ksaplabo-org/KsapSeatMotionSensor/img/システム構成図.png

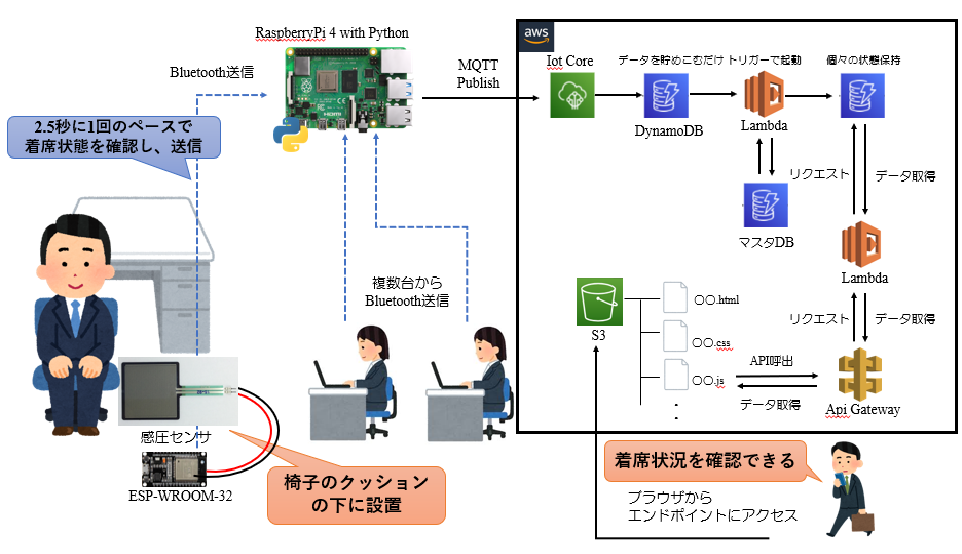
img/システム構成図.png
