ksaplabo-org/KsapSeatMotionSensor/img/感圧センサ.jpg

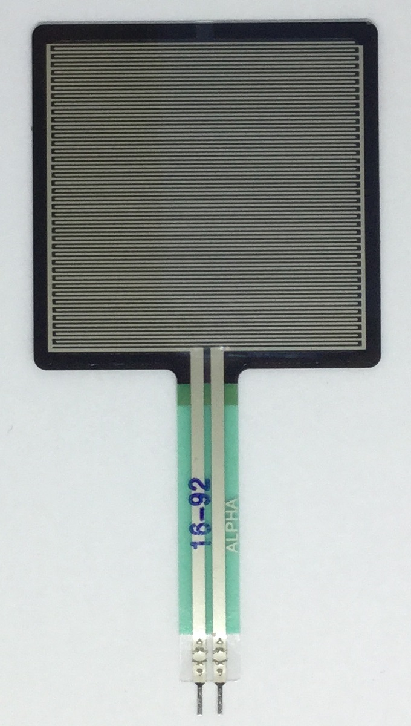
img/感圧センサ.jpg
