ksaplabo-org/KsapSeatMotionSensor/ksap-seatmotion/assets/img/外出.png

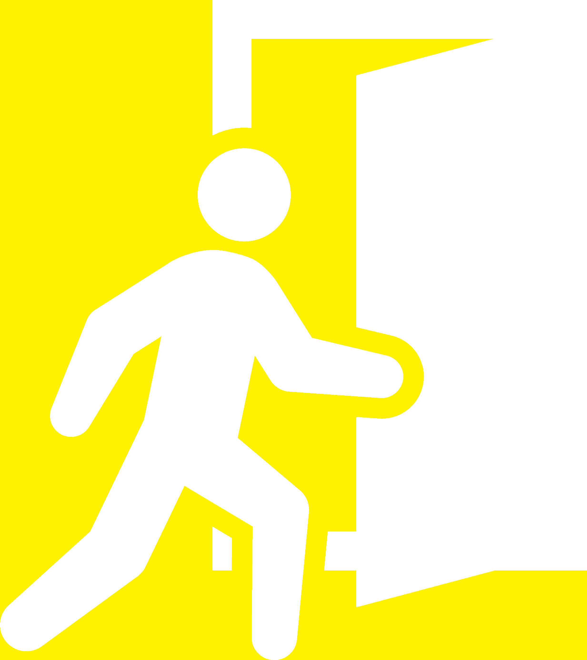
ksap-seatmotion/assets/img/外出.png
