ksaplabo-org/KsapSeatMotionSensor/ksap-seatmotion/assets/img/着席.png

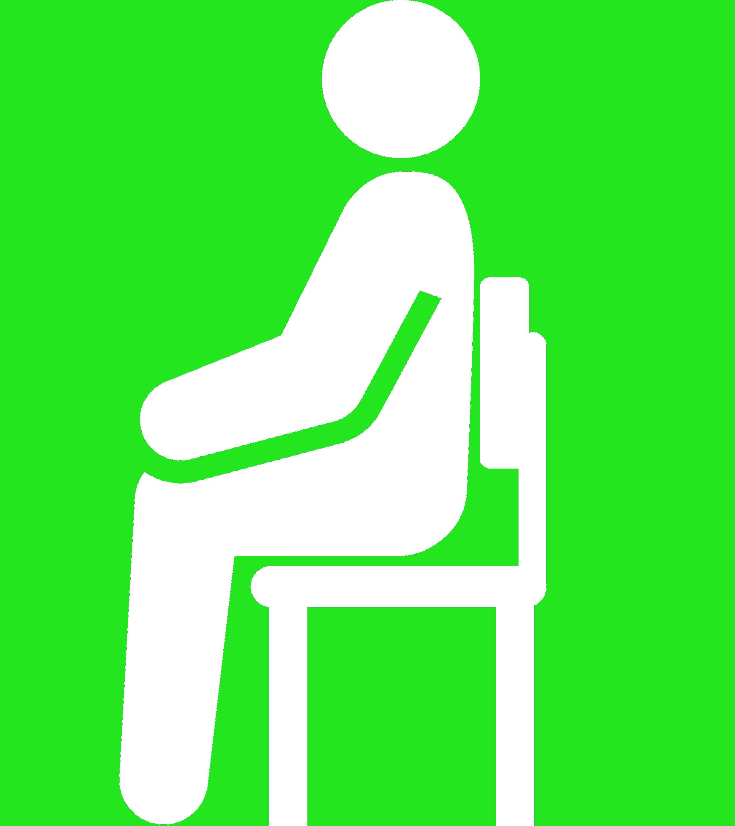
ksap-seatmotion/assets/img/着席.png
